croningp/dropfactory/media/img/platform/dropfactory_angle_view_2.jpg

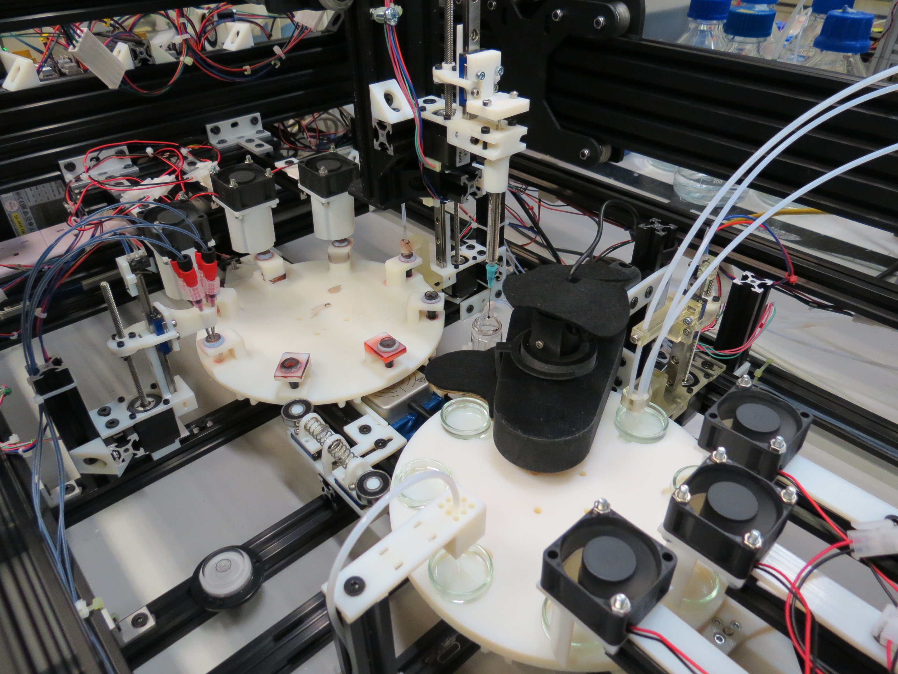
media/img/platform/dropfactory_angle_view_2.jpg
