croningp/dropfactory/media/img/platform/dropfactory_side_view.jpg

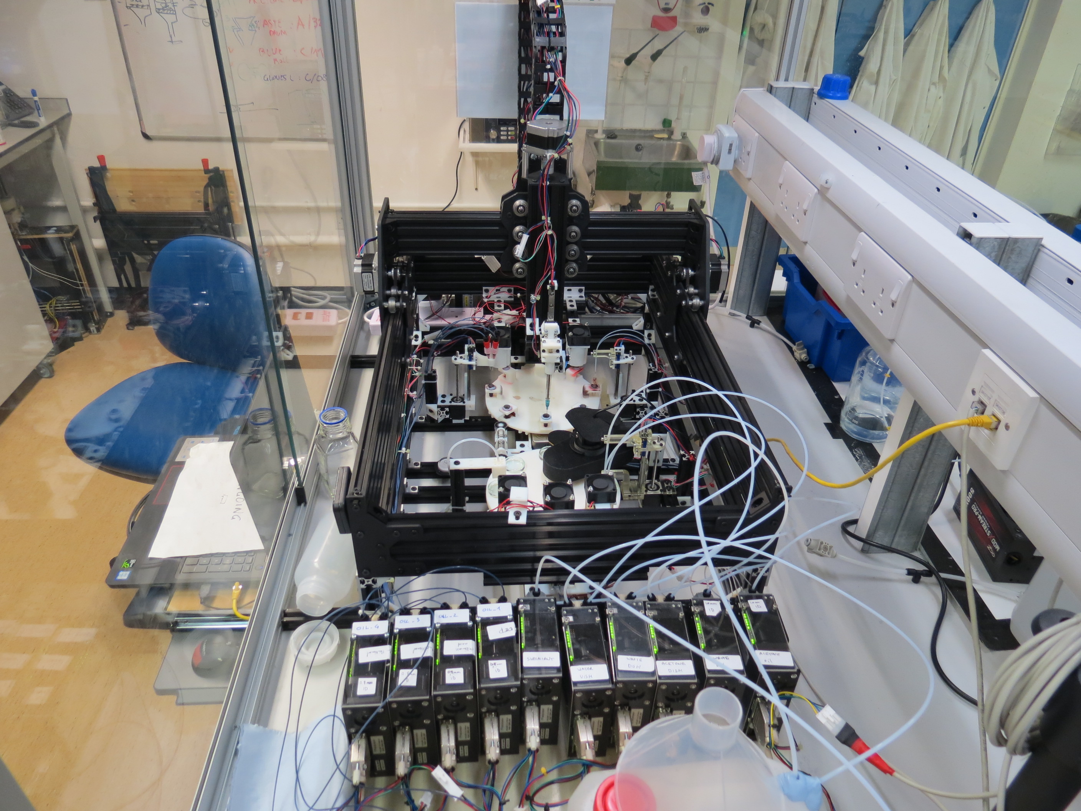
media/img/platform/dropfactory_side_view.jpg
