croningp/dropfactory/media/img/platform/dropfactory_side_view_2.jpg

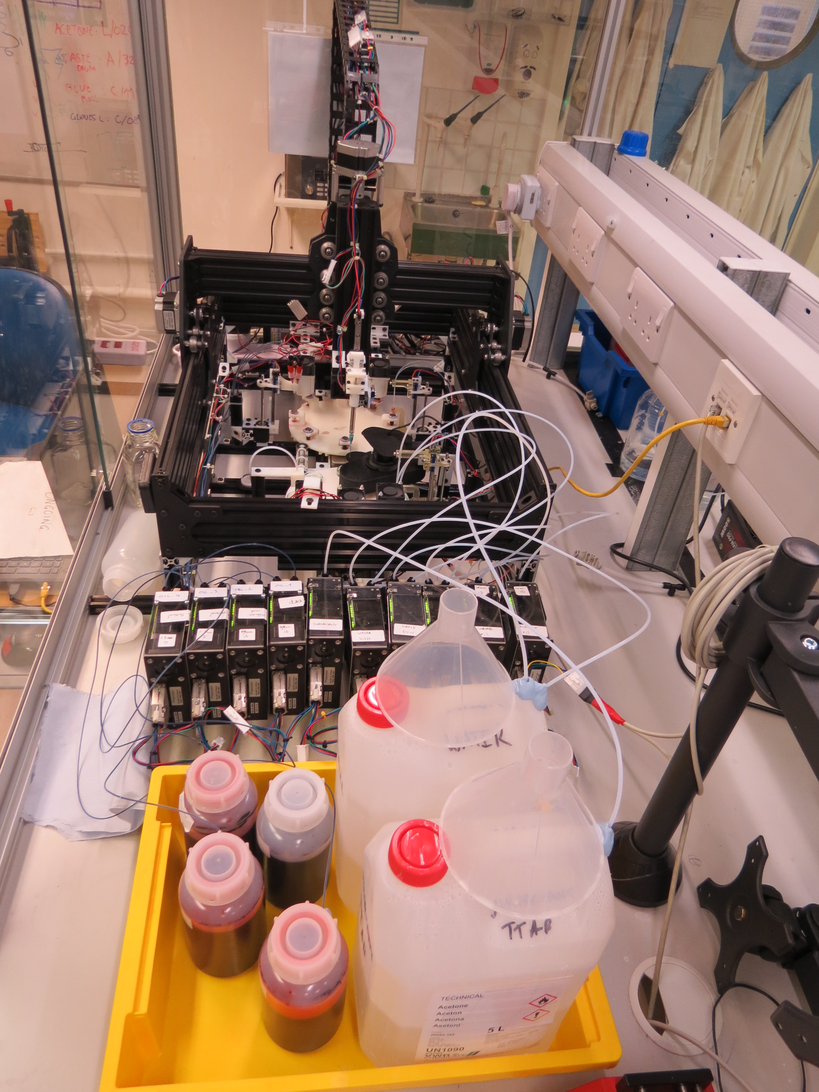
media/img/platform/dropfactory_side_view_2.jpg
