croningp/dropfactory/media/img/platform/pump_and_reageants.jpg

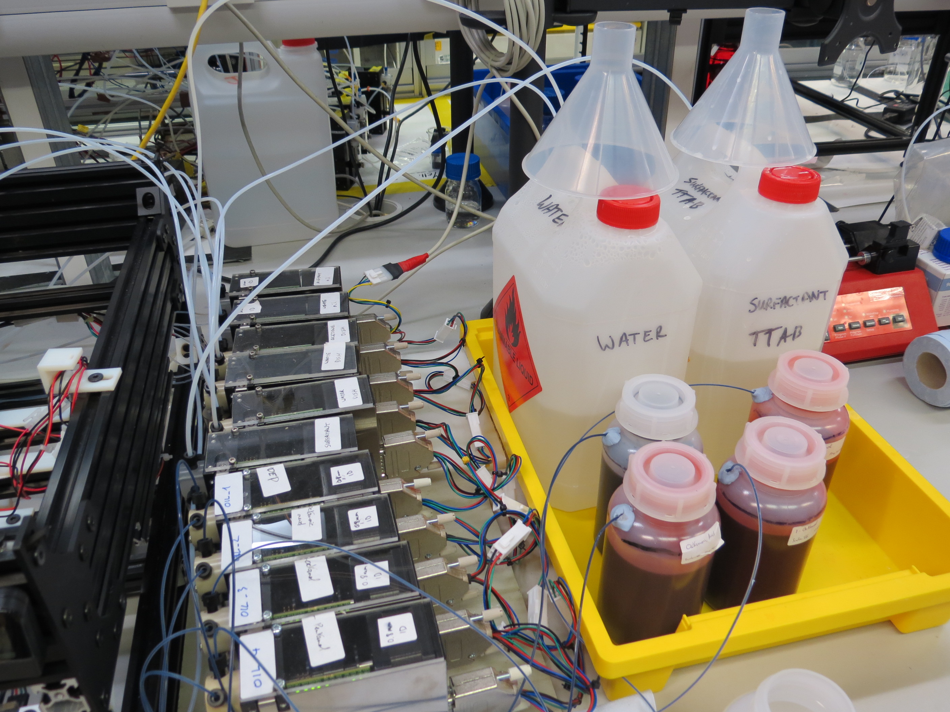
media/img/platform/pump_and_reageants.jpg
