croningp/dropfactory/media/img/syringe/syringe_angle.jpg

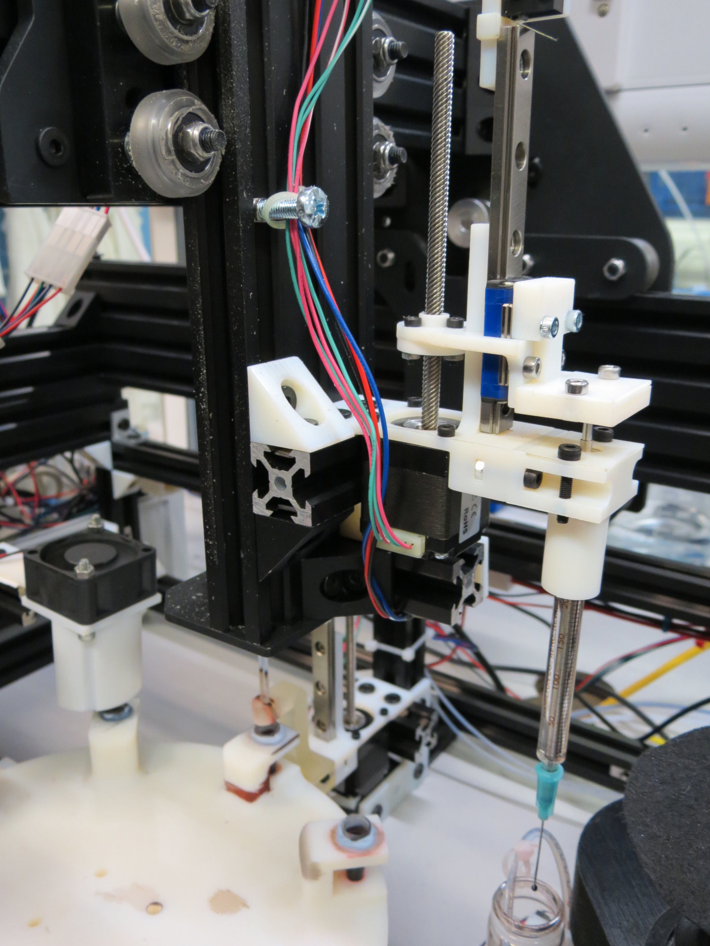
media/img/syringe/syringe_angle.jpg
