croningp/dropfactory/media/img/syringe/syringe_back.jpg

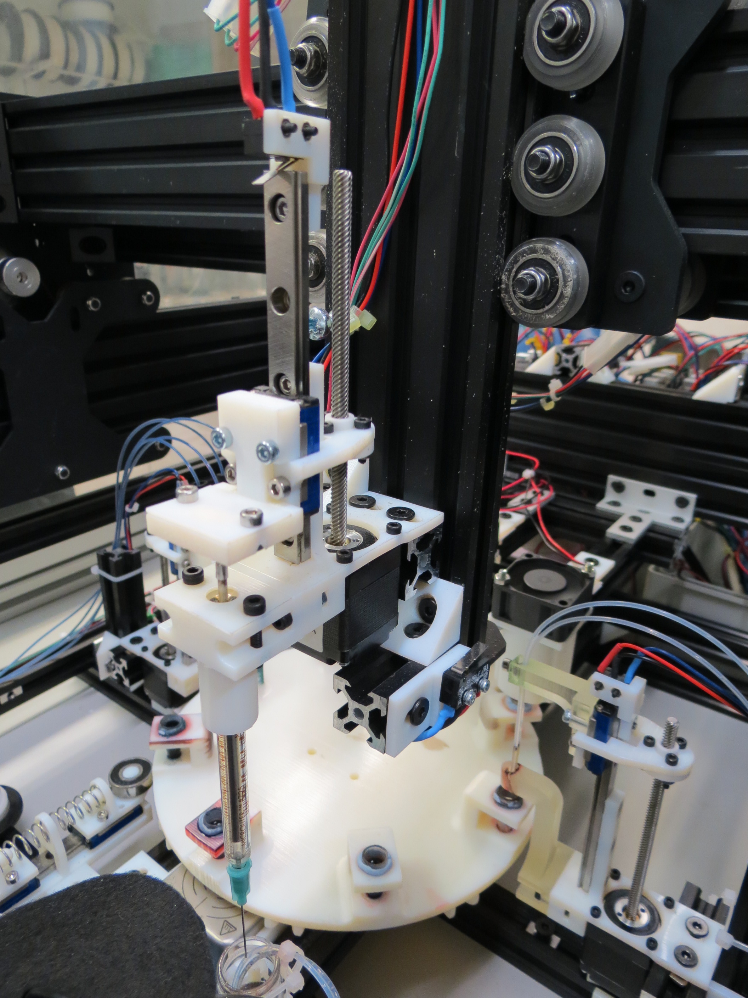
media/img/syringe/syringe_back.jpg
