croningp/dropfactory/media/img/various/cable_chain_holder.jpg

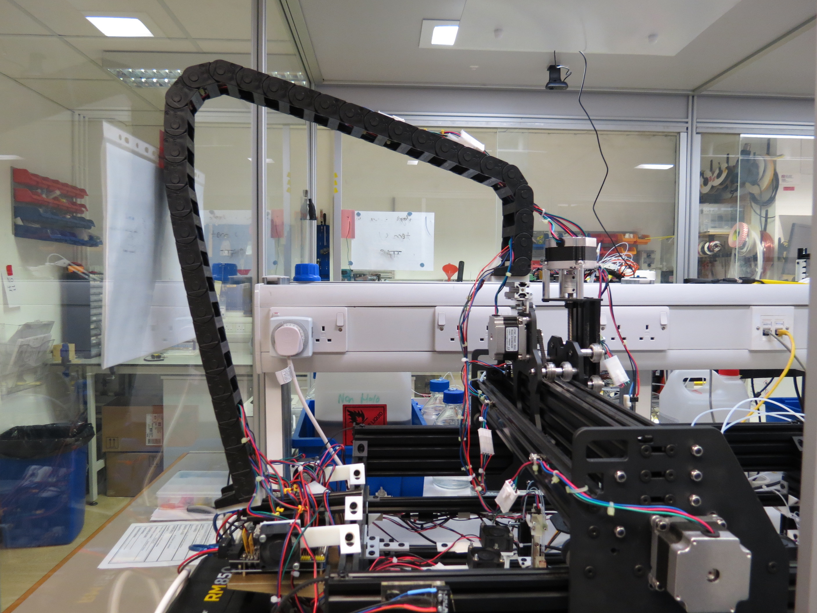
media/img/various/cable_chain_holder.jpg
