croningp/dropfactory/media/img/various/computer_control.jpg

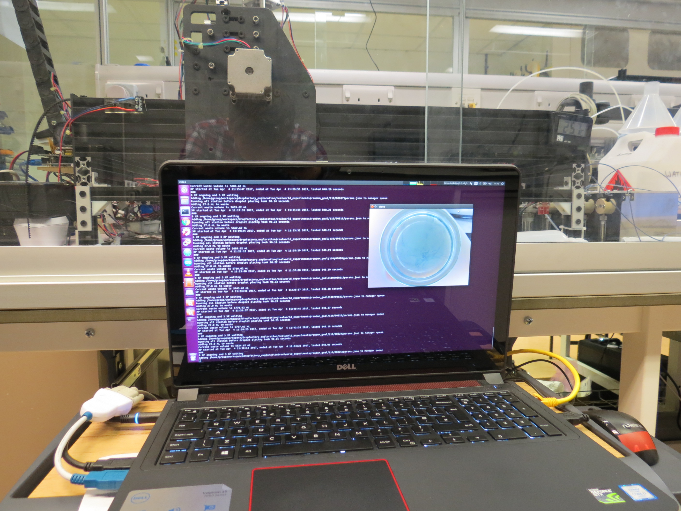
media/img/various/computer_control.jpg
