croningp/dropfactory/media/img/various/end_stop.jpg

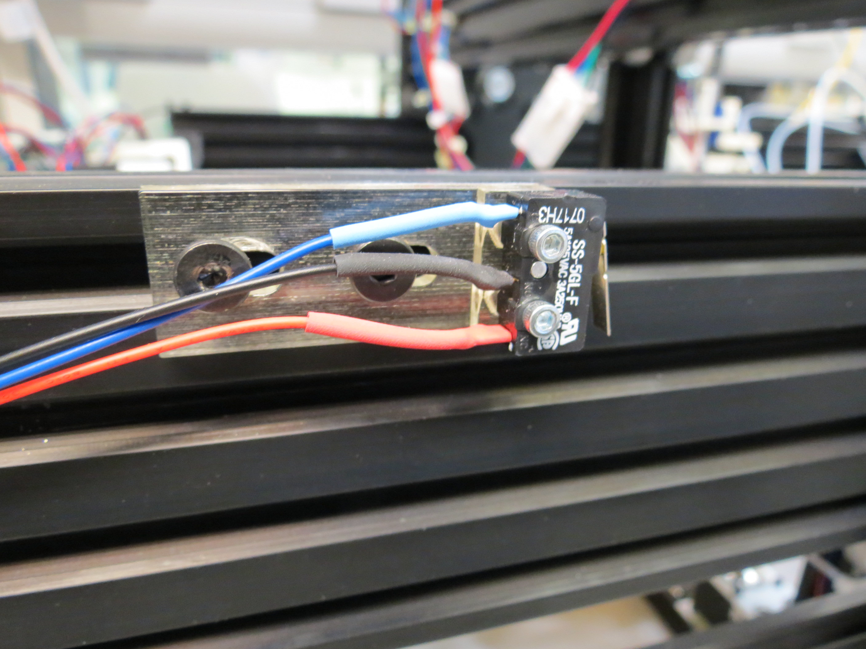
media/img/various/end_stop.jpg
