croningp/dropfactory/media/img/various/end_stop_2.jpg

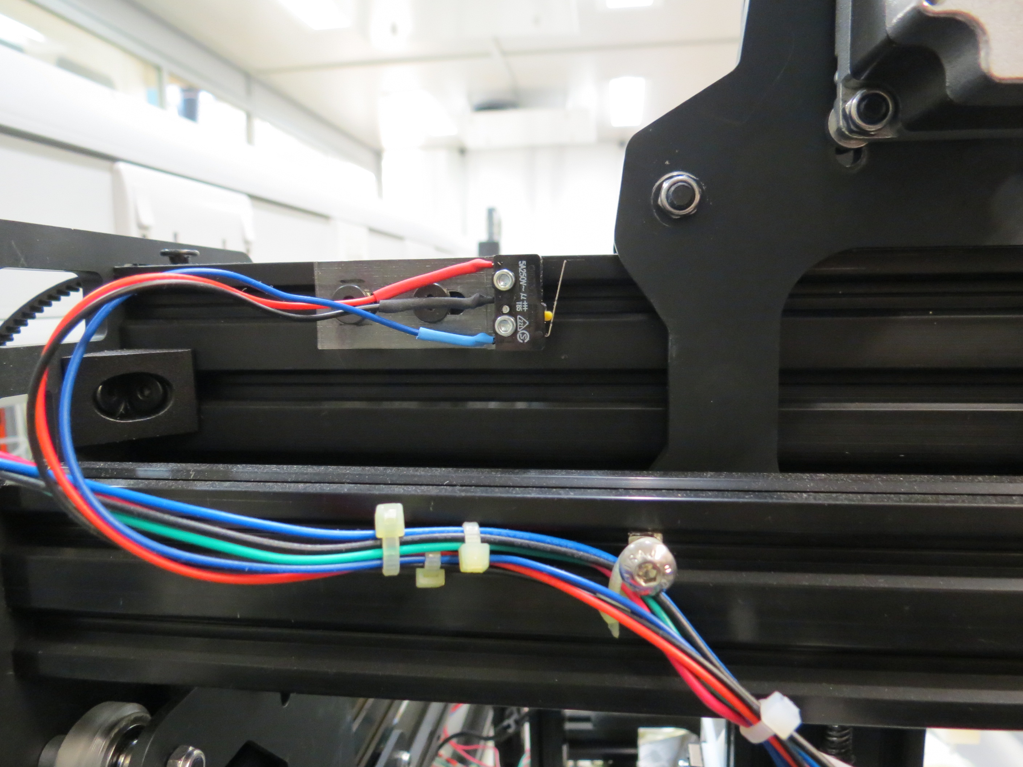
media/img/various/end_stop_2.jpg
