croningp/dropfactory/media/img/various/ramps_front.jpg

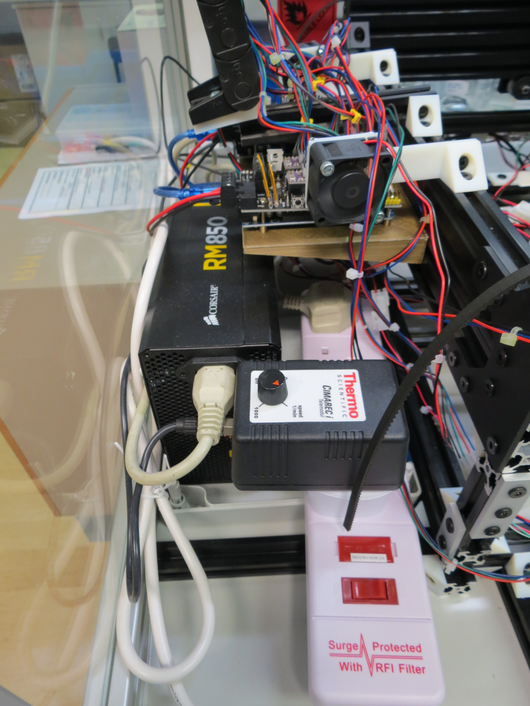
media/img/various/ramps_front.jpg
