croningp/dropfactory/media/img/various/ramps_side.jpg

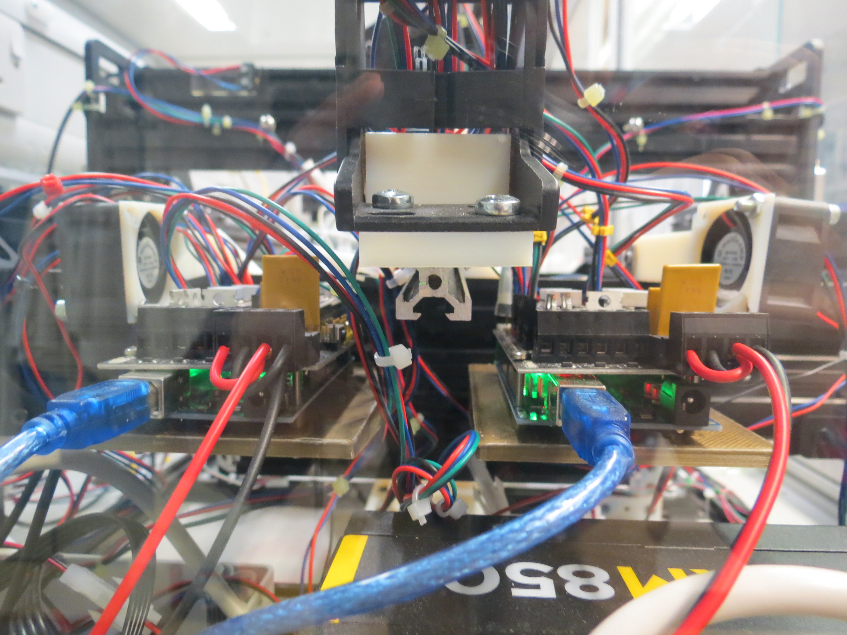
media/img/various/ramps_side.jpg
