croningp/dropfactory/media/img/various/ramps_top.jpg

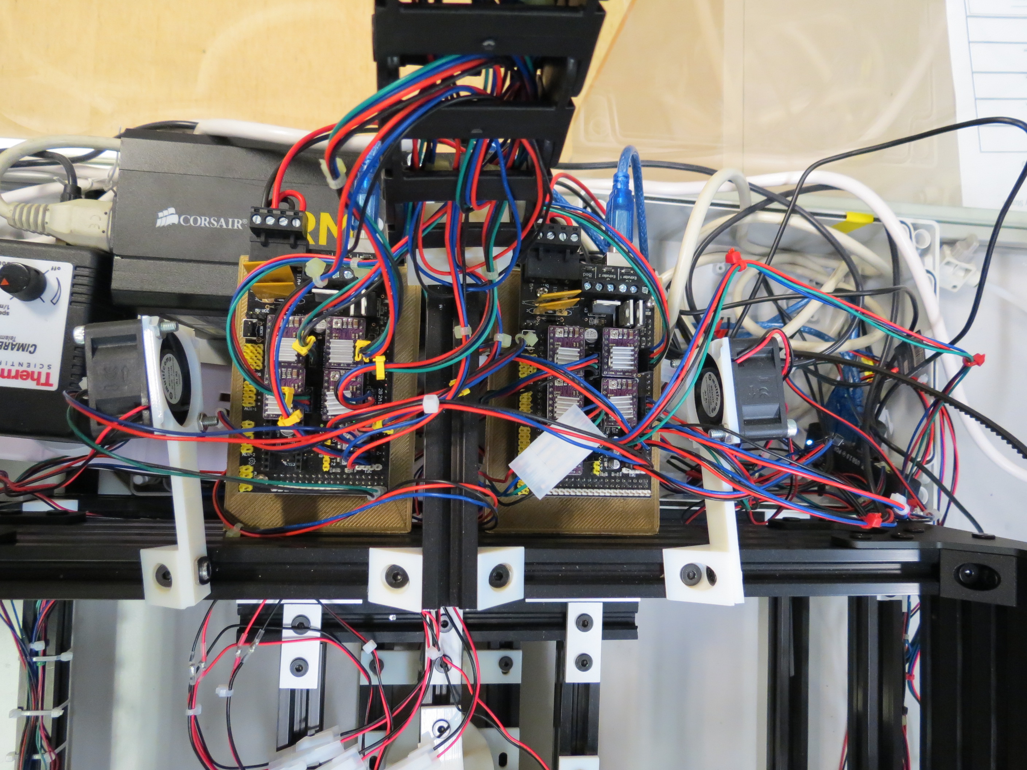
media/img/various/ramps_top.jpg
