croningp/dropfactory/media/img/various/reageants_storage.jpg

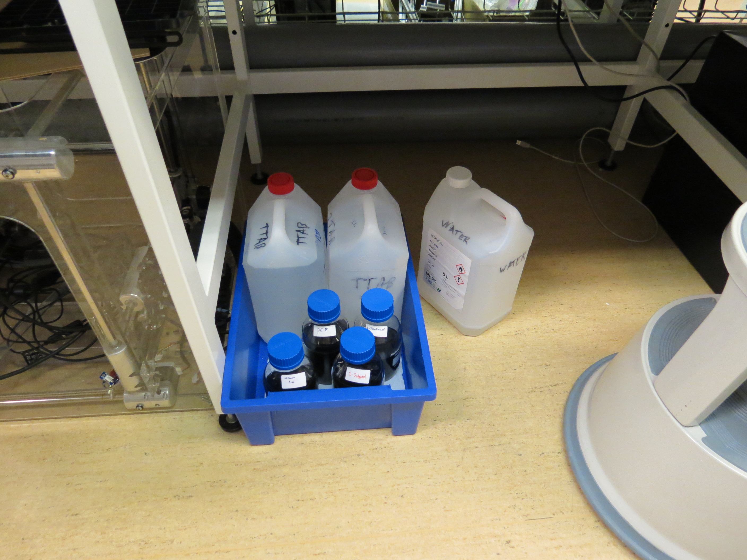
media/img/various/reageants_storage.jpg
