croningp/dropfactory/media/img/various/view_from_side.jpg

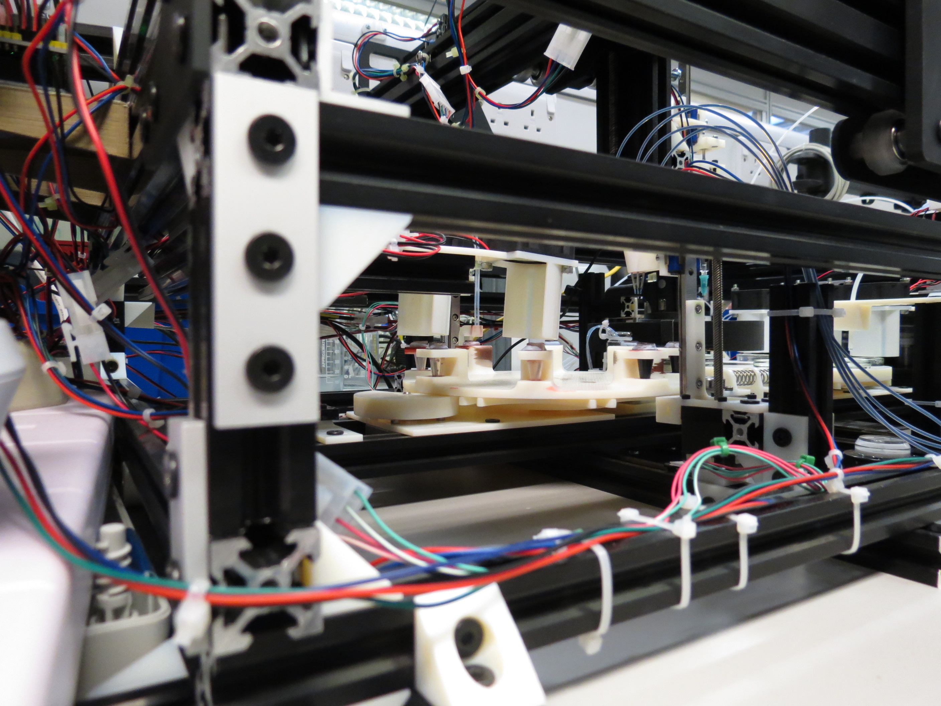
media/img/various/view_from_side.jpg
