croningp/dropfactory/media/img/various/wire_mess.jpg

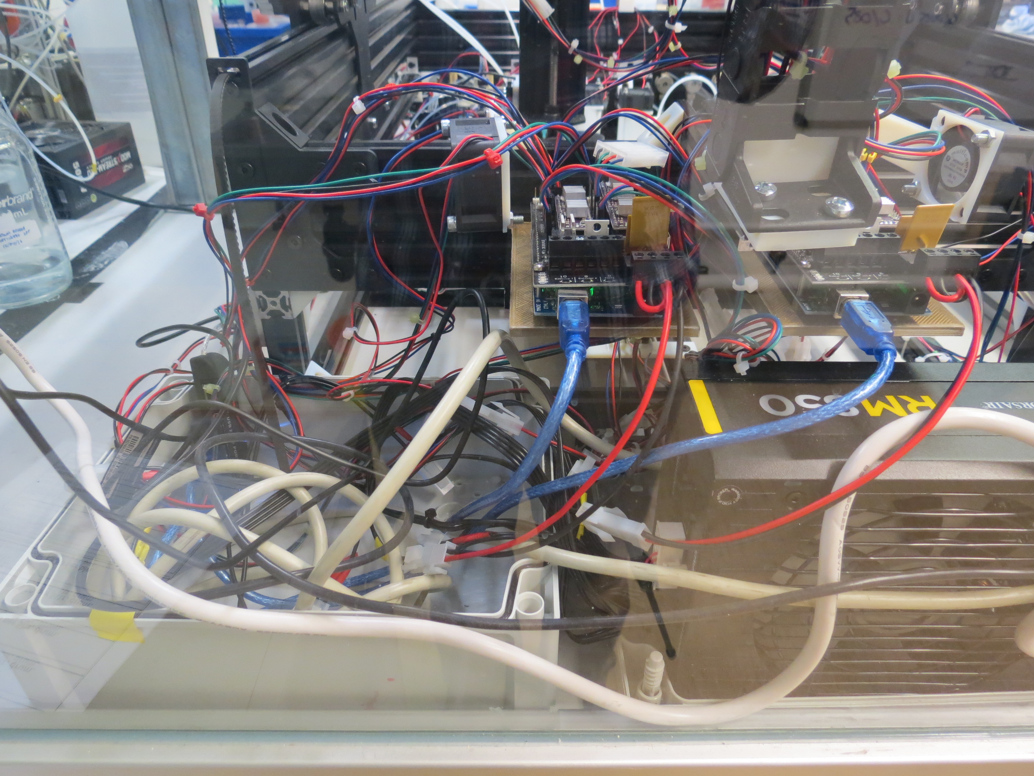
media/img/various/wire_mess.jpg
