croningp/dropfactory/media/img/various/z_axis_top.jpg

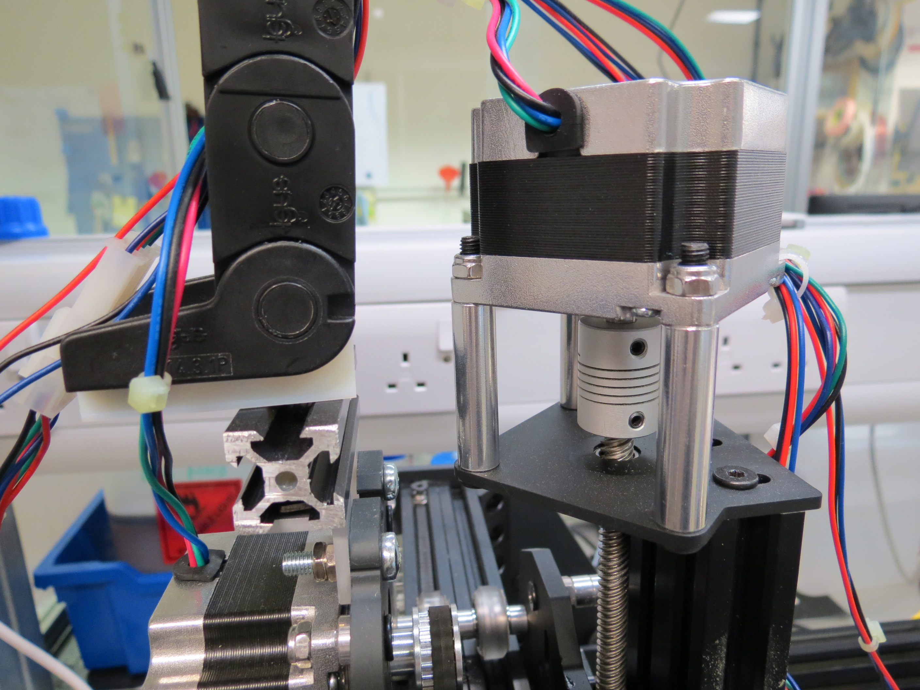
media/img/various/z_axis_top.jpg
