croningp/dropfactory/hardware/3d_parts/camera_holder/camera_holder_top.png

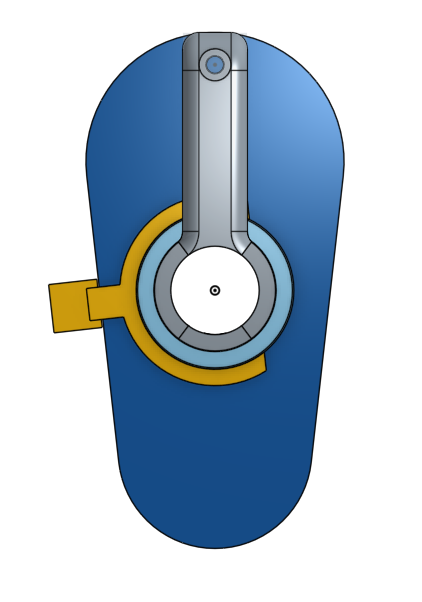
hardware/3d_parts/camera_holder/camera_holder_top.png
