croningp/dropfactory/hardware/3d_parts/oil_filling/oil_filler_angle.png

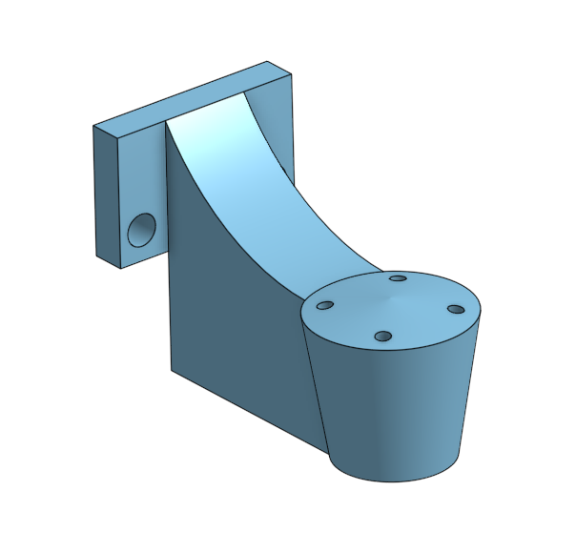
hardware/3d_parts/oil_filling/oil_filler_angle.png
