croningp/dropfactory/hardware/3d_parts/various/ramps_holder.png

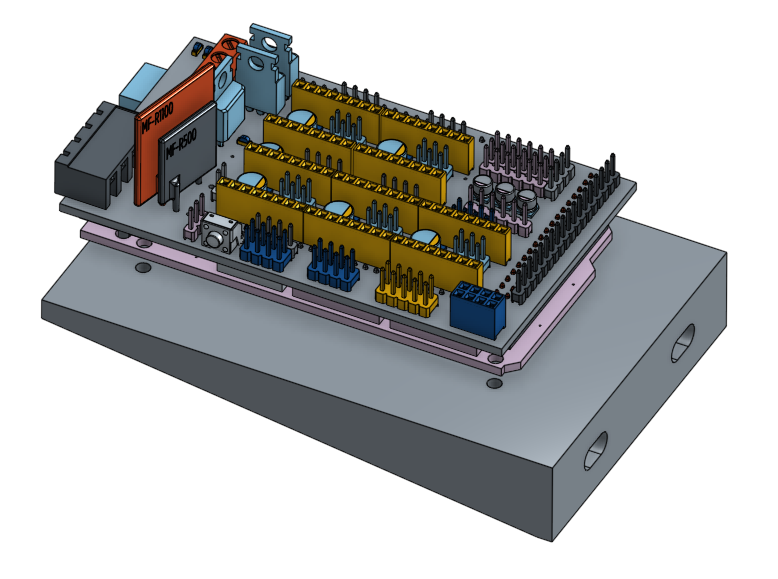
hardware/3d_parts/various/ramps_holder.png
