croningp/dropfactory/hardware/3d_parts/various/SHT15_holder.png

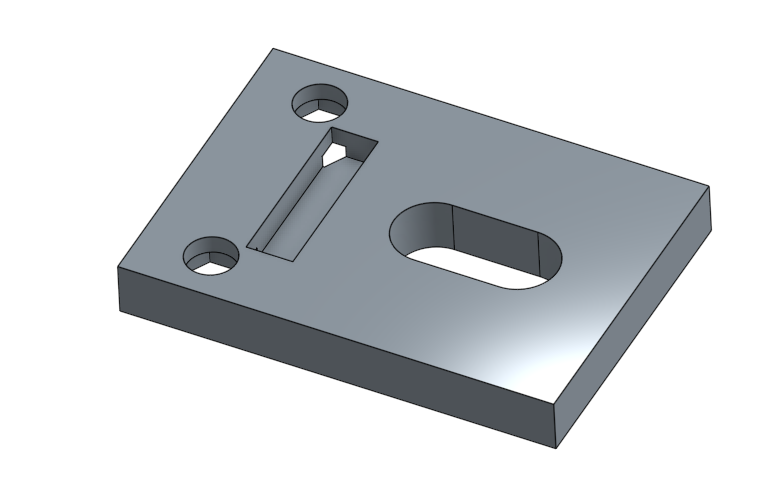
hardware/3d_parts/various/SHT15_holder.png
