croningp/dropfactory/hardware/3d_parts/various/vial_holder.png

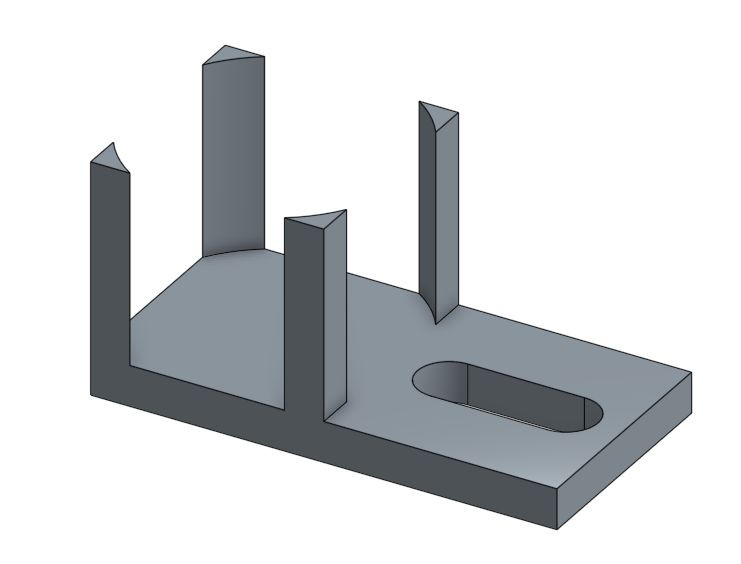
hardware/3d_parts/various/vial_holder.png
