croningp/dropfactory/hardware/3d_parts/camera_holder/camera_stand.stl

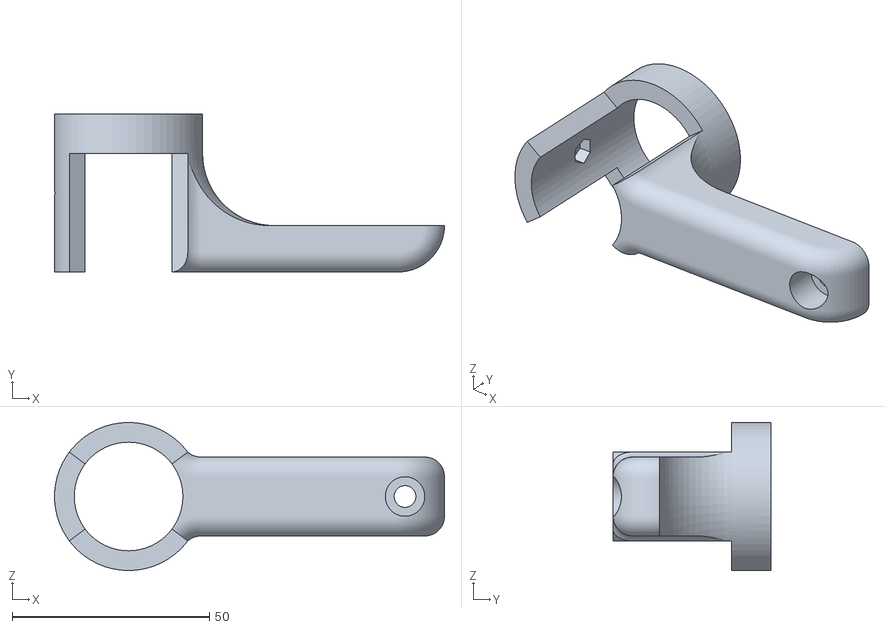
[picture p72: CAD file, 2017-06-06]
hardware/3d_parts/camera_holder/camera_stand.stl
98.7 x 40.0 x 37.5
