croningp/dropfactory/hardware/3d_parts/geneva_wheel/Geneva Wheel - light_damper.stl

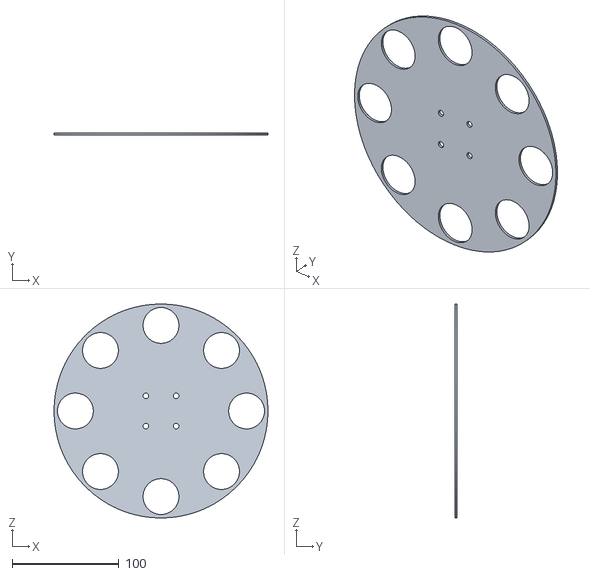
[picture p73: CAD file, 2017-06-06]
hardware/3d_parts/geneva_wheel/Geneva Wheel - light_damper.stl
200.0 x 2.00 x 200.0
