croningp/dropfactory/hardware/3d_parts/various/chain_rotation_holder.stl

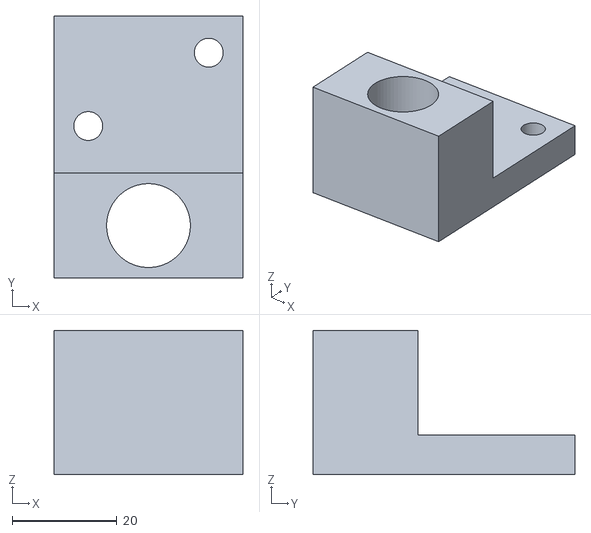
[picture p74: CAD file, 2017-06-06]
hardware/3d_parts/various/chain_rotation_holder.stl
36.0 x 50.0 x 27.5
