croningp/dropfactory/hardware/3d_parts/camera_holder/camera_shader.stl

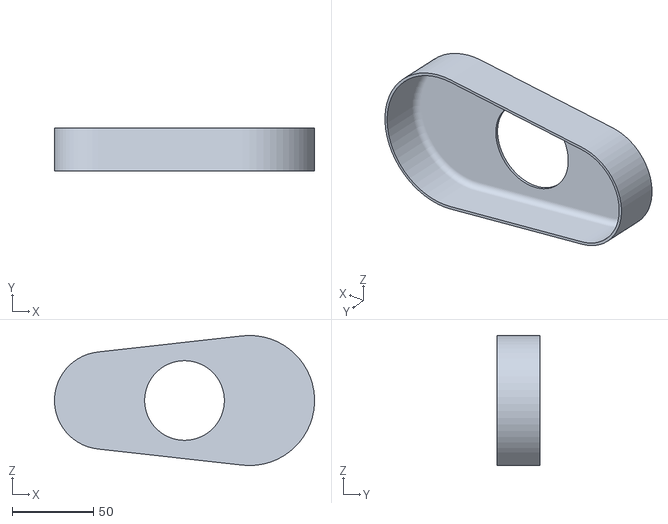
[picture p75: CAD file, 2017-06-06]
hardware/3d_parts/camera_holder/camera_shader.stl
159.9 x 26.5 x 80.0
