croningp/dropfactory/hardware/3d_parts/geneva_wheel/Geneva Wheel - geneva_wheel.stl

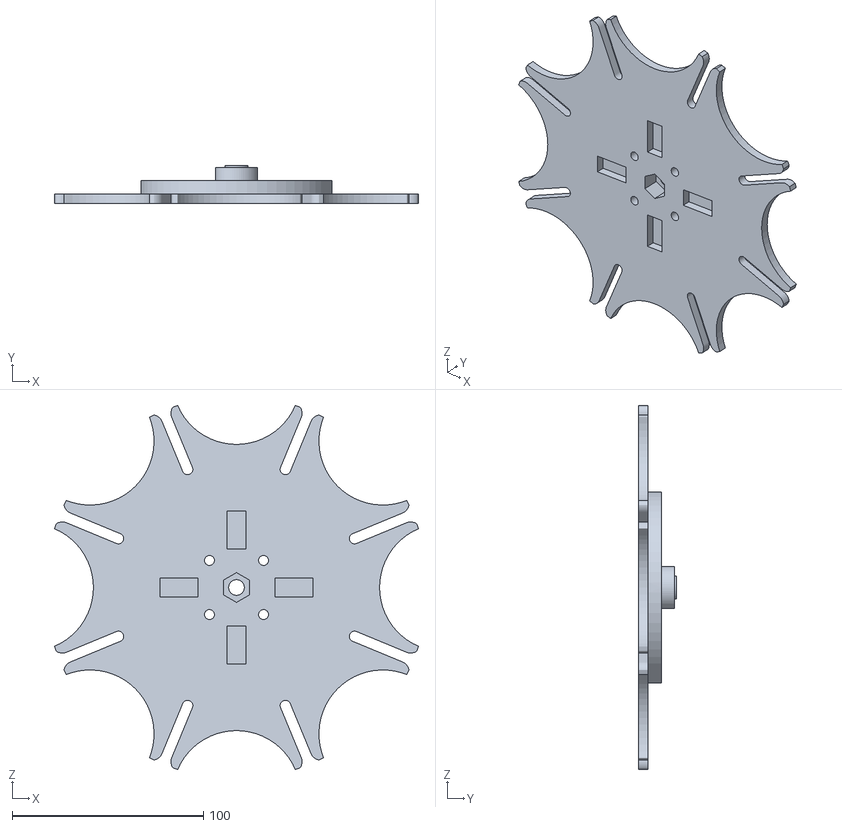
[picture p76: CAD file, 2017-06-06]
hardware/3d_parts/geneva_wheel/Geneva Wheel - geneva_wheel.stl
190.3 x 20.0 x 190.3
