croningp/dropfactory/hardware/3d_parts/various/switch_holder_inline_short.stl

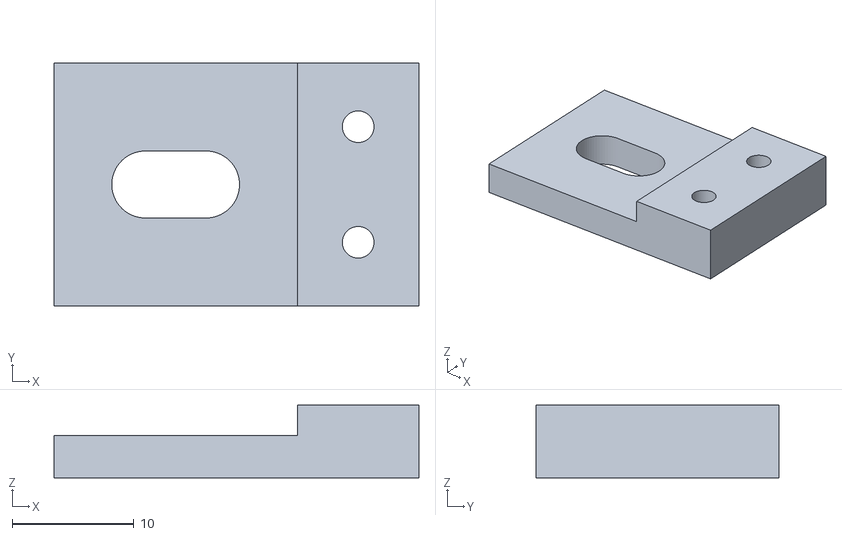
[picture p77: CAD file, 2017-06-06]
hardware/3d_parts/various/switch_holder_inline_short.stl
30.0 x 20.0 x 6.00
