croningp/dropfactory/hardware/3d_parts/geneva_wheel/Geneva Wheel - petri_dish_top.stl

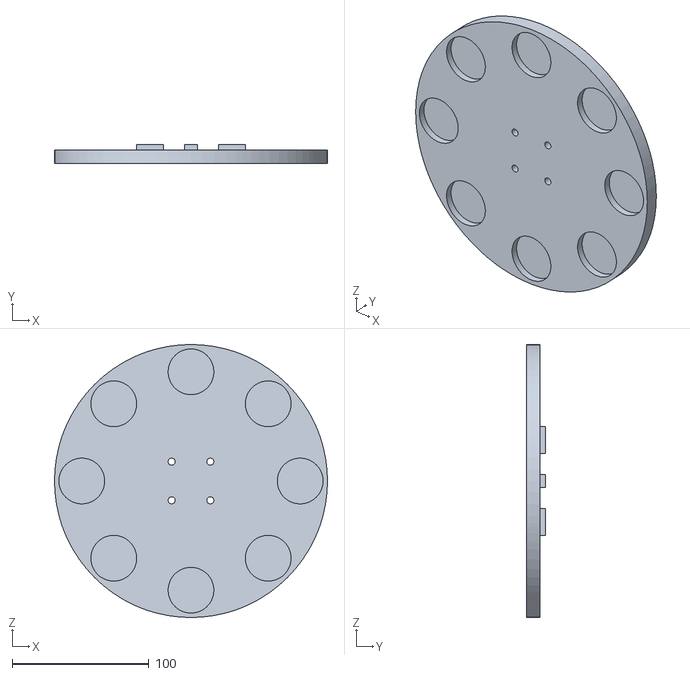
[picture p78: CAD file, 2017-06-06]
hardware/3d_parts/geneva_wheel/Geneva Wheel - petri_dish_top.stl
200.0 x 14.0 x 200.0
