croningp/dropfactory/hardware/3d_parts/various/switch_holder_inline_long.stl

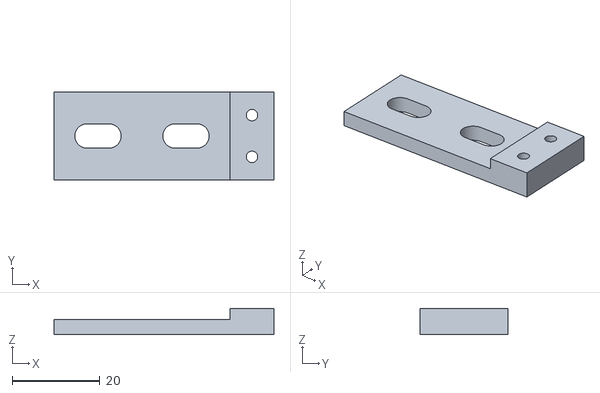
[picture p79: CAD file, 2017-06-06]
hardware/3d_parts/various/switch_holder_inline_long.stl
50.0 x 20.0 x 6.00
