croningp/dropfactory/hardware/3d_parts/geneva_wheel/Geneva Wheel Stabilizer - cariage.stl

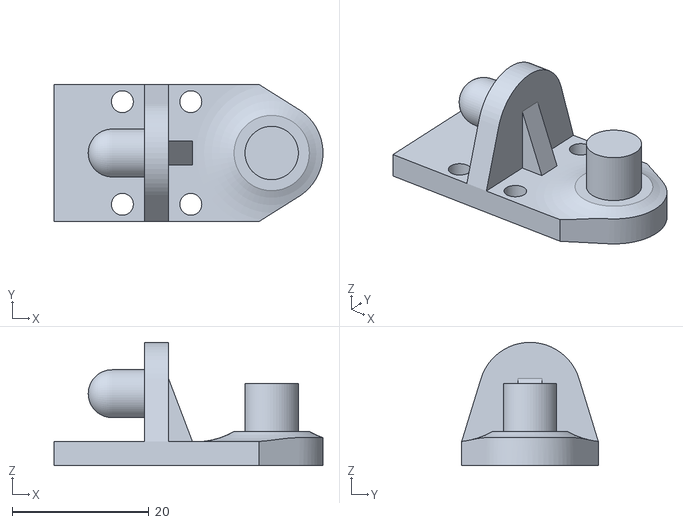
[picture p80: CAD file, 2017-06-06]
hardware/3d_parts/geneva_wheel/Geneva Wheel Stabilizer - cariage.stl
39.3 x 20.0 x 18.0
