croningp/dropfactory/hardware/3d_parts/various/vslot_corner_side.stl

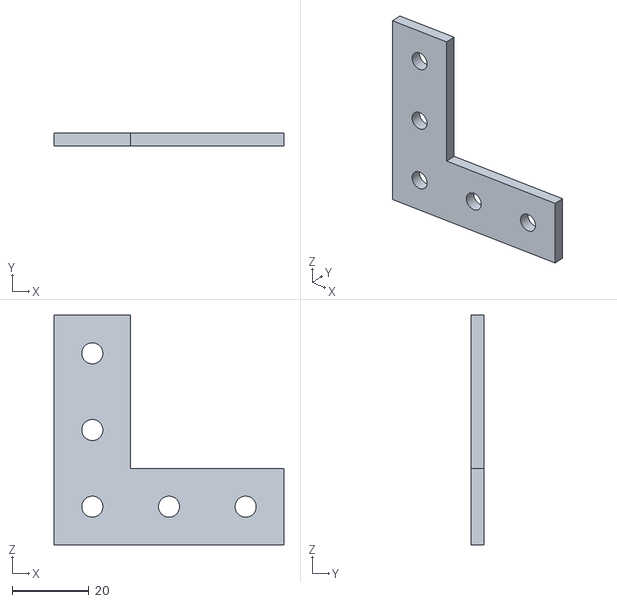
[picture p81: CAD file, 2017-06-06]
hardware/3d_parts/various/vslot_corner_side.stl
60.0 x 3.50 x 60.0
