croningp/dropfactory/hardware/3d_parts/geneva_wheel/Geneva Wheel Stabilizer - body.stl

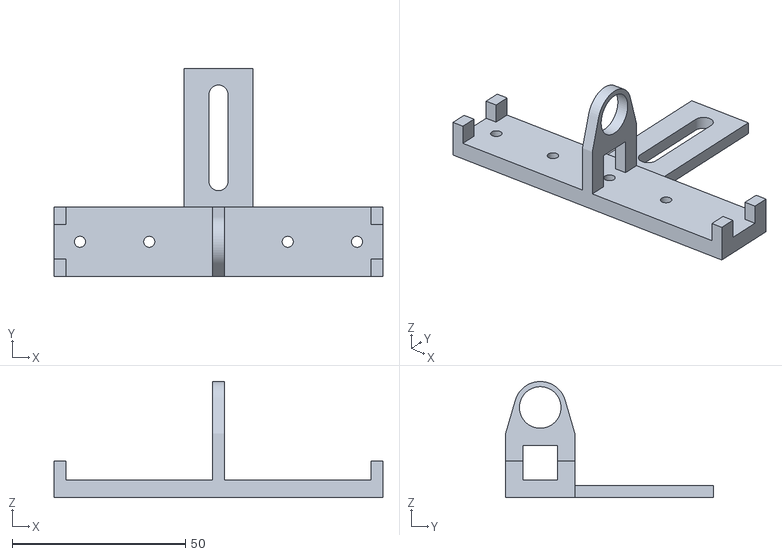
[picture p82: CAD file, 2017-06-06]
hardware/3d_parts/geneva_wheel/Geneva Wheel Stabilizer - body.stl
95.0 x 60.0 x 33.5
