croningp/dropfactory/hardware/3d_parts/various/evaporator.stl

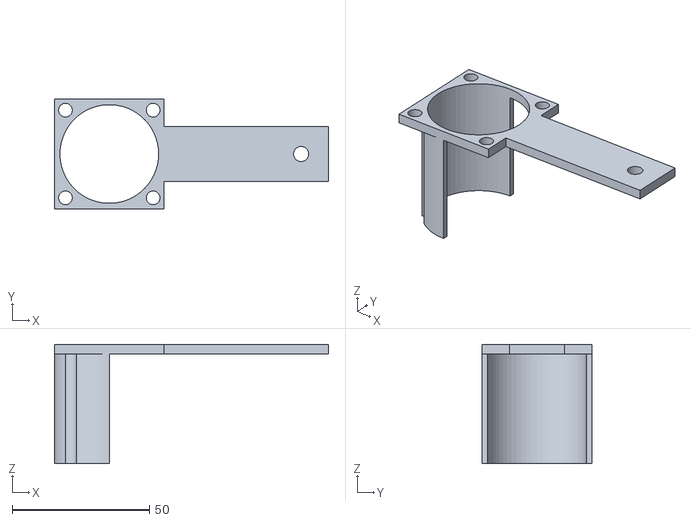
[picture p83: CAD file, 2017-06-06]
hardware/3d_parts/various/evaporator.stl
100.0 x 40.0 x 43.5
