croningp/dropfactory/hardware/3d_parts/geneva_wheel/Geneva Wheel - switch_holder.stl

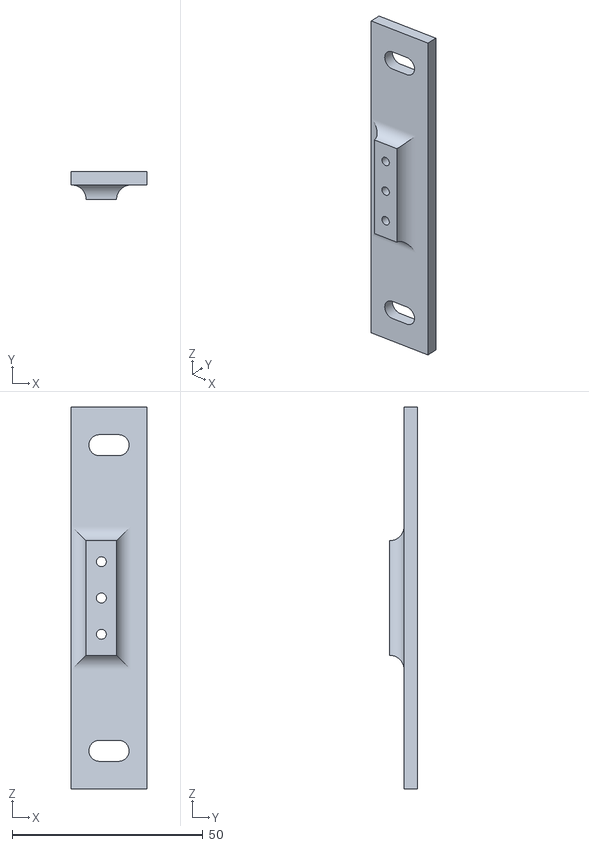
[picture p84: CAD file, 2017-06-06]
hardware/3d_parts/geneva_wheel/Geneva Wheel - switch_holder.stl
20.0 x 7.25 x 100.0
