croningp/dropfactory/hardware/3d_parts/various/chain_rotation_axis.stl

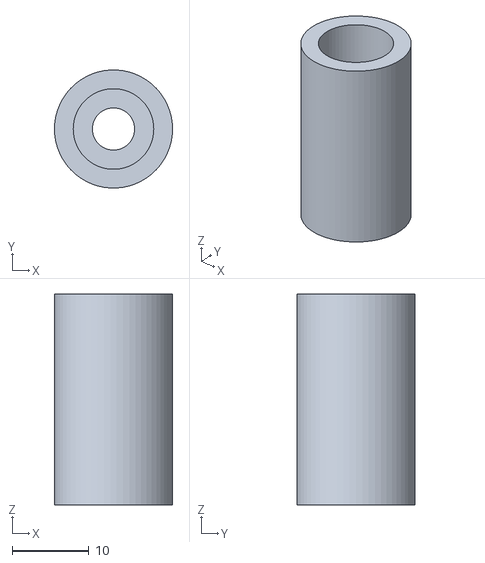
[picture p85: CAD file, 2017-06-06]
hardware/3d_parts/various/chain_rotation_axis.stl
15.4 x 15.4 x 27.5
