croningp/dropfactory/hardware/3d_parts/various/vslot_cable_guide.stl

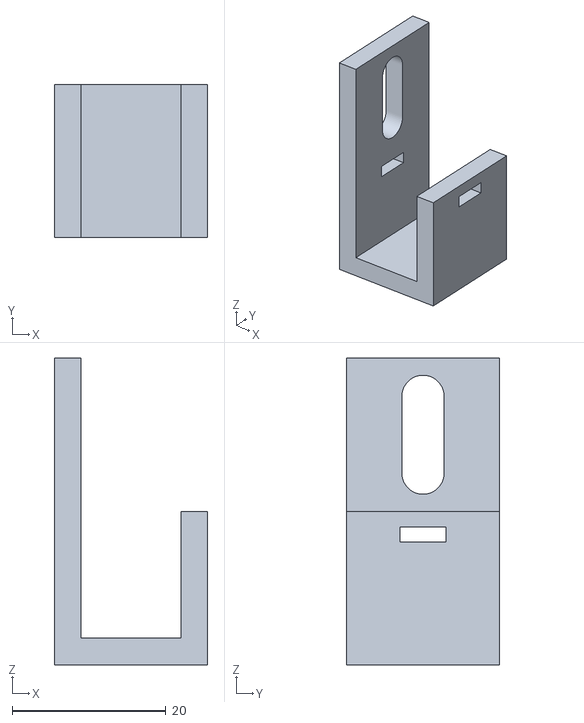
[picture p86: CAD file, 2017-06-06]
hardware/3d_parts/various/vslot_cable_guide.stl
20.0 x 20.0 x 40.0
