croningp/dropfactory/hardware/3d_parts/geneva_wheel/Geneva Wheel - vslot_mount.stl

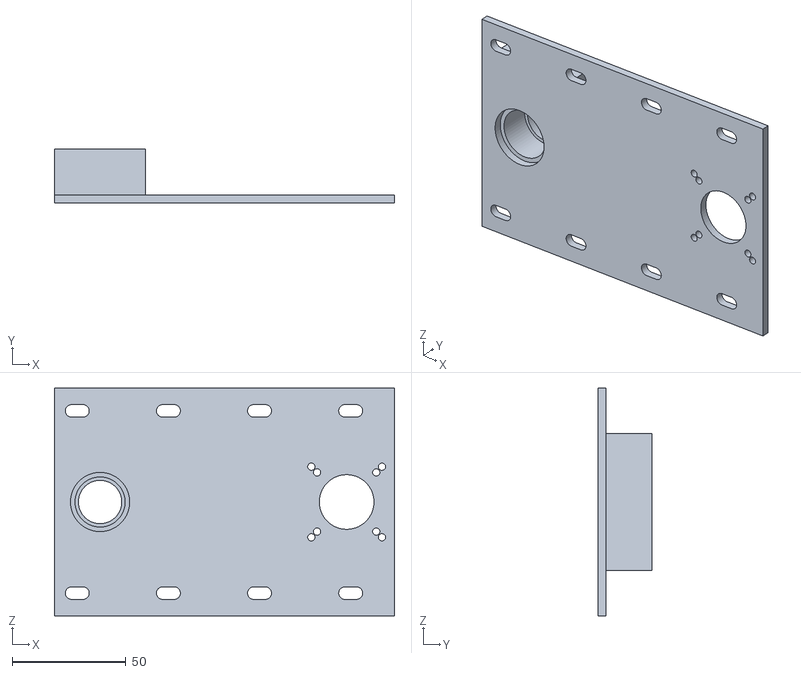
[picture p87: CAD file, 2017-06-06]
hardware/3d_parts/geneva_wheel/Geneva Wheel - vslot_mount.stl
149.2 x 23.5 x 100.0
