croningp/dropfactory/hardware/3d_parts/various/ SHT15_holder.stl

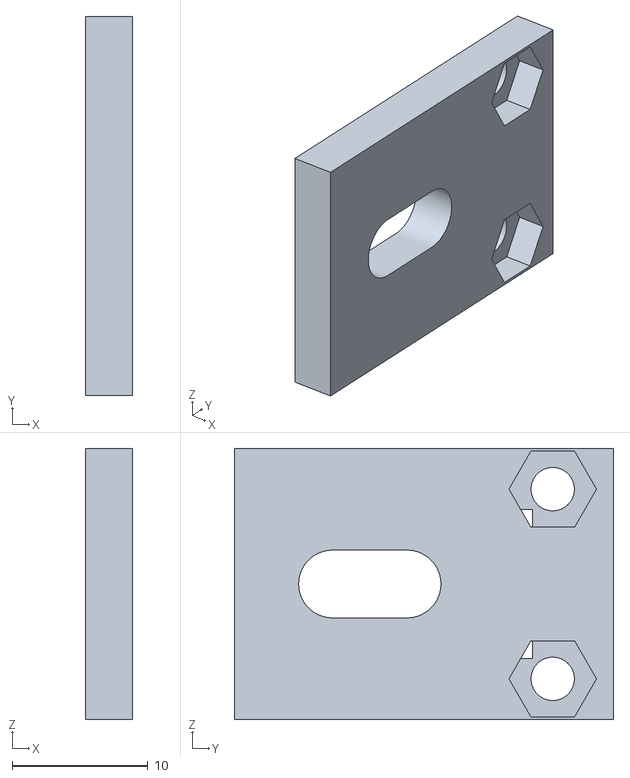
[picture p88: CAD file, 2017-06-06]
hardware/3d_parts/various/ SHT15_holder.stl
3.50 x 28.0 x 20.0
