croningp/dropfactory/hardware/3d_parts/geneva_wheel/Geneva Wheel - mixing_pot_top.stl

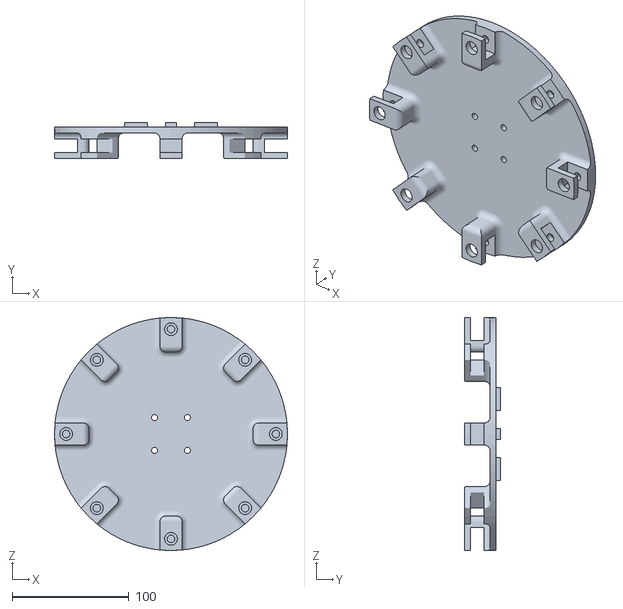
[picture p89: CAD file, 2017-06-06]
hardware/3d_parts/geneva_wheel/Geneva Wheel - mixing_pot_top.stl
200.0 x 31.0 x 200.0
