croningp/dropfactory/hardware/3d_parts/various/vslot_flat_corner_length_2.stl

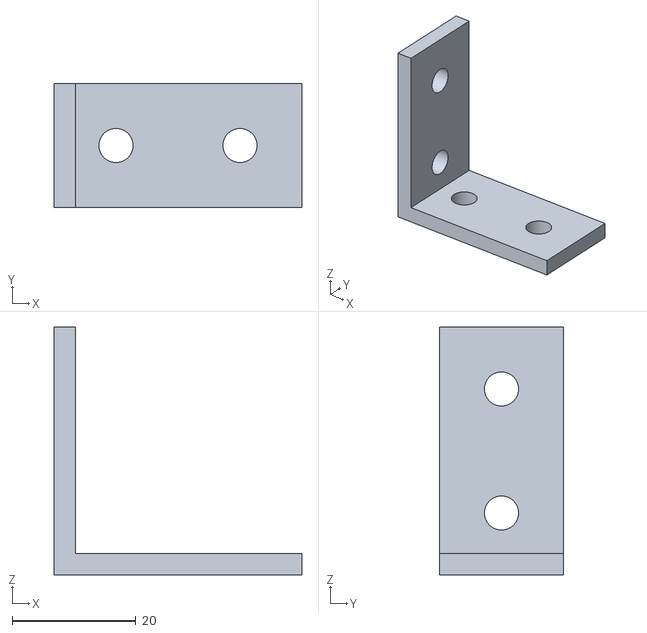
[picture p90: CAD file, 2017-06-06]
hardware/3d_parts/various/vslot_flat_corner_length_2.stl
40.0 x 20.0 x 40.0
