croningp/dropfactory/hardware/3d_parts/various/vial_holder.stl

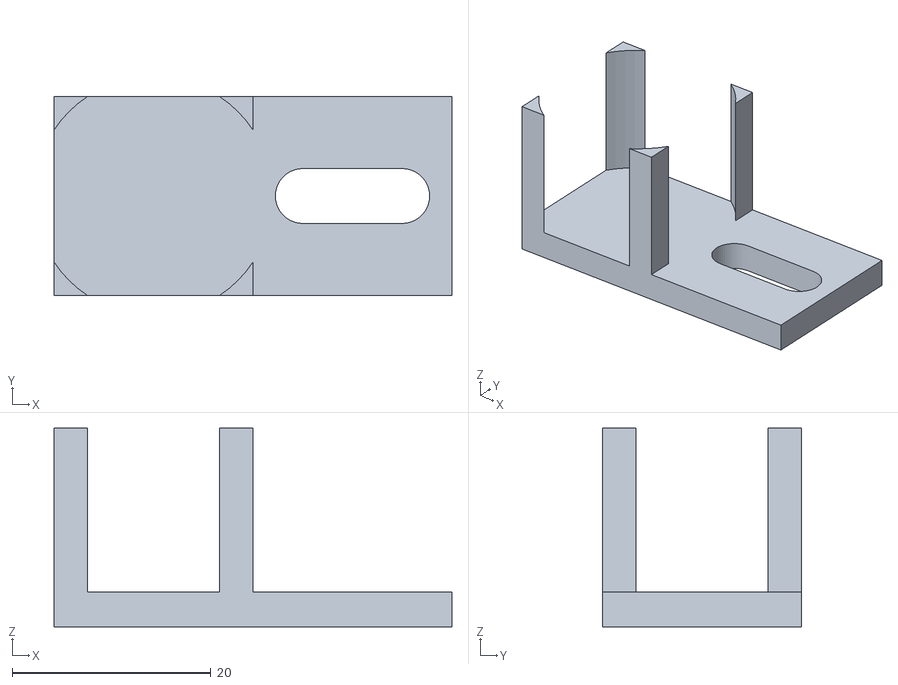
[picture p91: CAD file, 2017-06-06]
hardware/3d_parts/various/vial_holder.stl
40.0 x 20.0 x 20.0
