croningp/dropfactory/hardware/3d_parts/various/switch_holder_top_long.stl

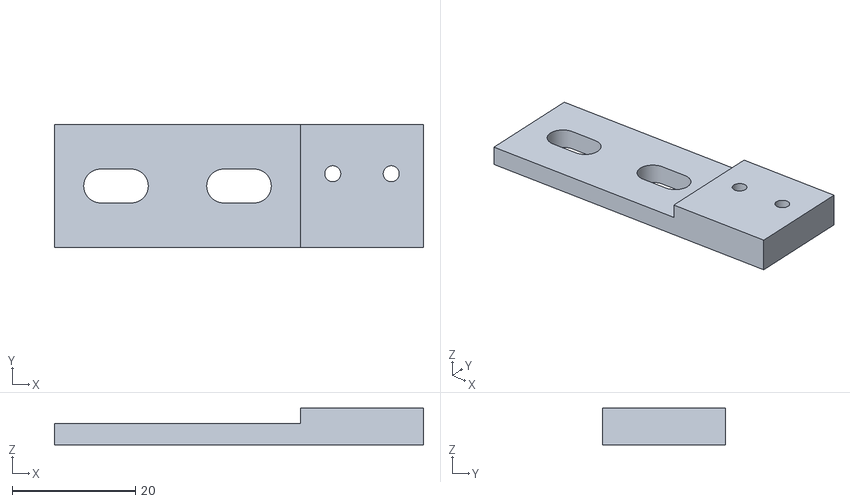
[picture p92: CAD file, 2017-06-06]
hardware/3d_parts/various/switch_holder_top_long.stl
60.0 x 20.0 x 6.00
