croningp/dropfactory/hardware/3d_parts/various/block.stl

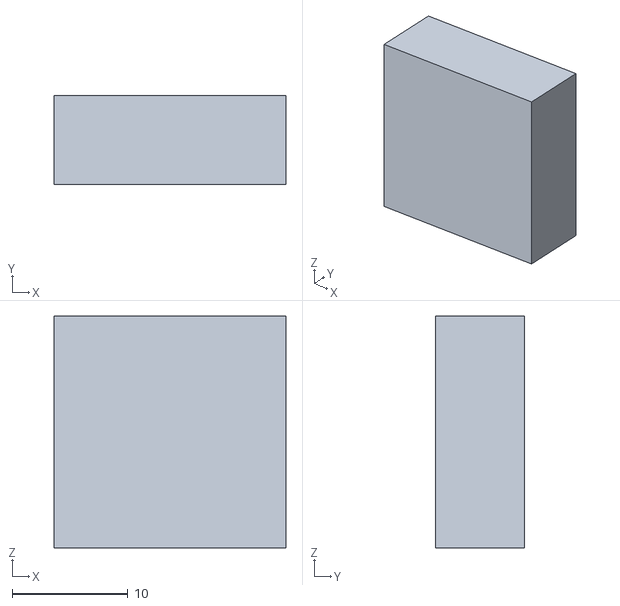
[picture p93: CAD file, 2016-06-13]
hardware/3d_parts/various/block.stl
20.0 x 7.70 x 20.0
