croningp/dropfactory/hardware/3d_parts/various/vslot_corner_basic.stl

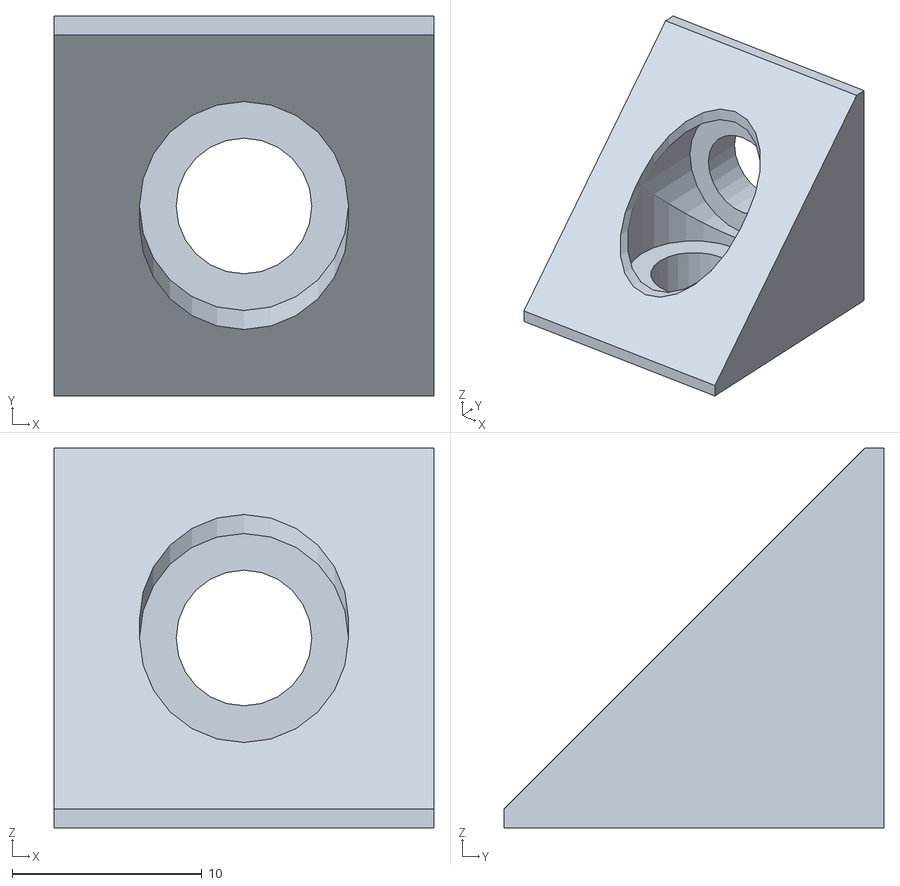
[picture p94: CAD file, 2016-02-03]
hardware/3d_parts/various/vslot_corner_basic.stl
20.0 x 20.0 x 20.0
