croningp/dropfactory/hardware/3d_parts/various/ramps_spacers.stl

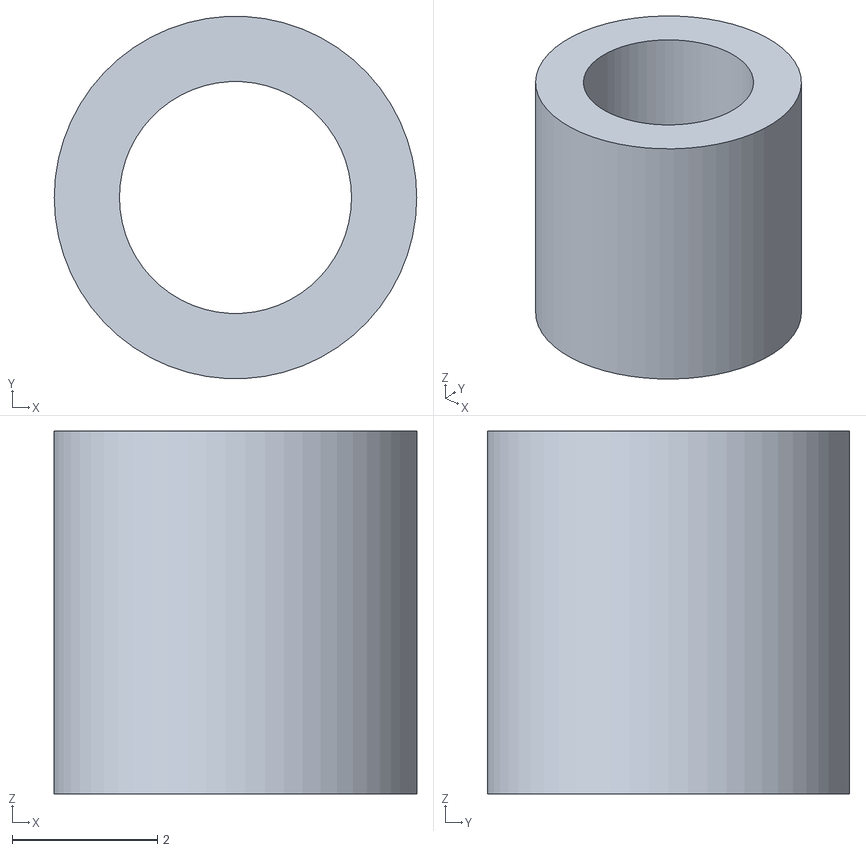
[picture p95: CAD file, 2016-02-01]
hardware/3d_parts/various/ramps_spacers.stl
5.00 x 4.99 x 5.00
